robegamesios/PipBoy3000/STL/PipBoy_3000_Rotary_1.STL

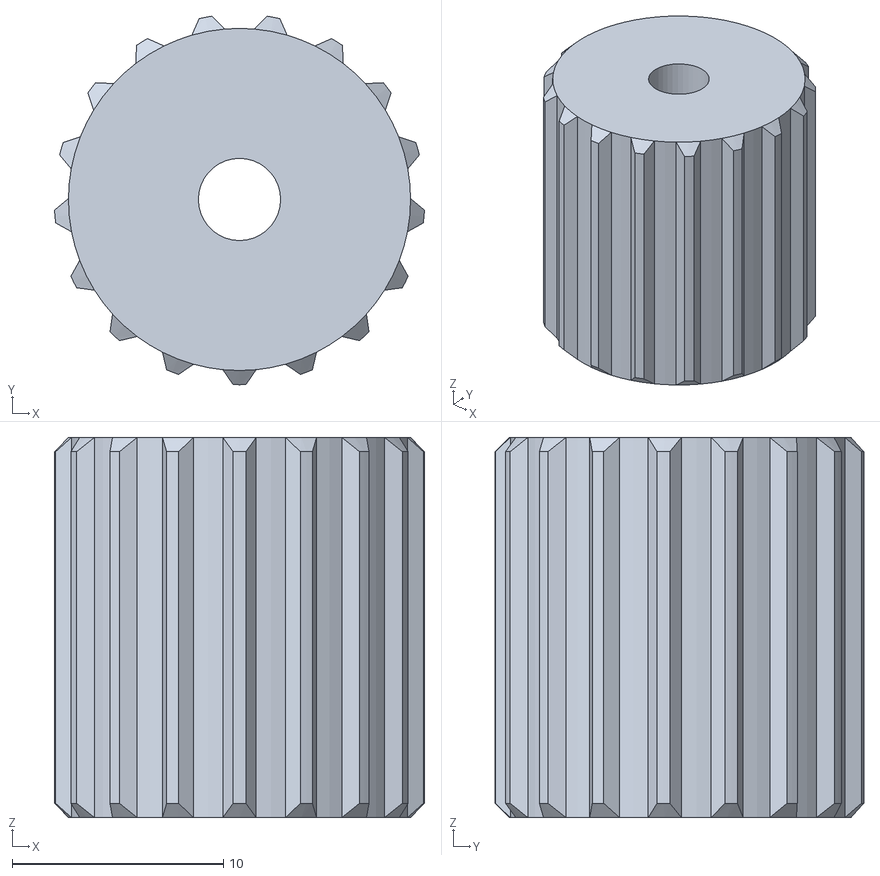
[picture p18: CAD file, 2025-01-02]
STL/PipBoy_3000_Rotary_1.STL
17.5 x 17.5 x 18.0
