robegamesios/PipBoy3000/STL/PipBoy_3000_Front-4inch.stl

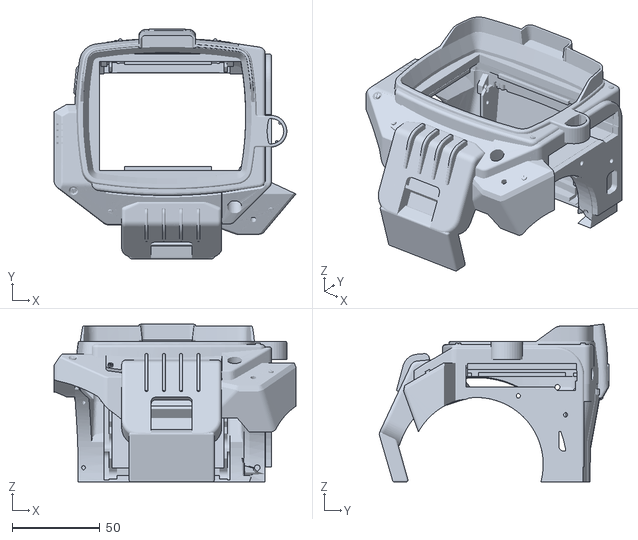
[picture p19: CAD file, 2025-01-02]
STL/PipBoy_3000_Front-4inch.stl
138.1 x 131.0 x 90.2
